mandraga/TeslaBMS/BMSUtil.h

#include <Arduino.h>
#include "Logger.h"

class BMSUtil {    
public:
    
    static uint8_t genCRC(uint8_t *input, int lenInput)
    {
        uint8_t generator = 0x07;
        uint8_t crc = 0;
  
        for (int x = 0; x < lenInput; x++)
        {
            crc ^= input[x]; /* XOR-in the next input byte */

            for (int i = 0; i < 8; i++)
            {
                if ((crc & 0x80) != 0)
                {
                    crc = (uint8_t)((crc << 1) ^ generator);
                }
                else
                {
                    crc <<= 1;
                }
            }
        }

        return crc;
    }

    static void sendData(uint8_t *data, uint8_t dataLen, bool isWrite)
    {
        uint8_t orig = data[0];
        uint8_t addrByte = data[0];
        if (isWrite) addrByte |= 1;
        SERIALBMS.write(addrByte);
        SERIALBMS.write(&data[1], dataLen - 1);  //assumes that there are at least 2 bytes sent every time. There should be, addr and cmd at the least.
        data[0] = addrByte;
        if (isWrite) SERIALBMS.write(genCRC(data, dataLen));        

        if (Logger::isDebug())
        {
            SERIALCONSOLE.print("Sending: ");
            SERIALCONSOLE.print(addrByte, HEX);
            SERIALCONSOLE.print(" ");
            for (int x = 1; x < dataLen; x++) {
                SERIALCONSOLE.print(data[x], HEX);
                SERIALCONSOLE.print(" ");
            }
            if (isWrite) SERIALCONSOLE.print(genCRC(data, dataLen), HEX);
            SERIALCONSOLE.println();
        }
        
        data[0] = orig;
    }

    static int getReply(uint8_t *data, int maxLen)
    { 
        int numBytes = 0; 
        if (Logger::isDebug()) SERIALCONSOLE.print("Reply: ");
        while (SERIALBMS.available() && numBytes < maxLen)
        {
            data[numBytes] = SERIALBMS.read();
            if (Logger::isDebug()) {
                SERIALCONSOLE.print(data[numBytes], HEX);
                SERIALCONSOLE.print(" ");
            }
            numBytes++;
        }
        if (maxLen == numBytes)
        {
            while (SERIALBMS.available()) SERIALBMS.read();
        }
        if (Logger::isDebug()) SERIALCONSOLE.println();
        return numBytes;
    }
    
    //Uses above functions to send data then get the response. Will auto retry if response not 
    //the expected return length. This helps to alleviate any comm issues. The Due cannot exactly
    //match the correct comm speed so sometimes there are data glitches.
    static int sendDataWithReply(uint8_t *data, uint8_t dataLen, bool isWrite, uint8_t *retData, int retLen)
    {
        int attempts = 1;
        int returnedLength;
        while (attempts < 4)
        {
            sendData(data, dataLen, isWrite);
            delay(2 * ((retLen / 8) + 1));
            returnedLength = getReply(retData, retLen);
            if (returnedLength == retLen) return returnedLength;
            attempts++;
        }
        return returnedLength; //failed to get a proper response.
    }
};
